oe5rnl/ESP32-ATT-C-LVGL8/docs/att_foto_bestueckt.jpg

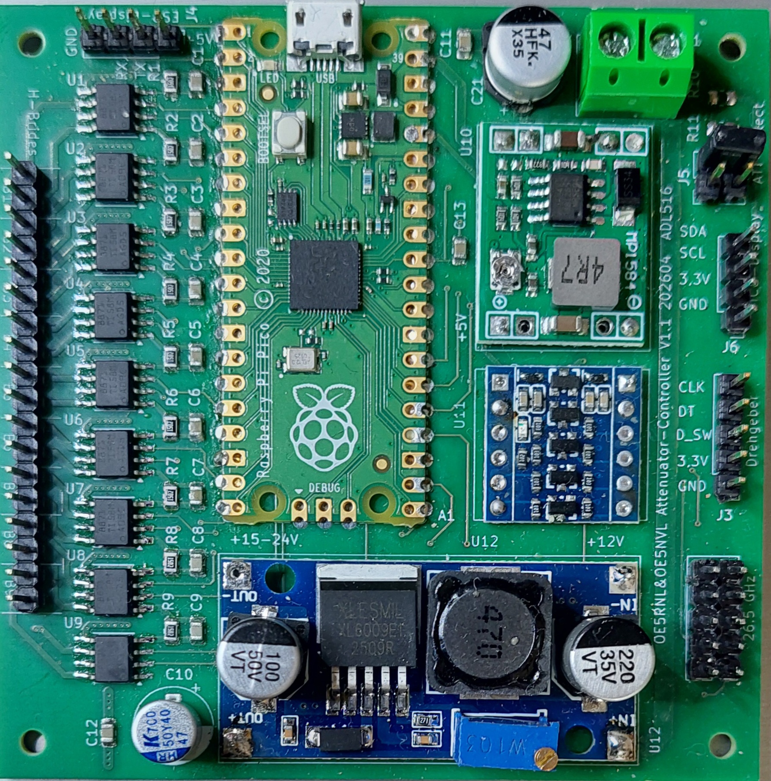
docs/att_foto_bestueckt.jpg
