oe5rnl/ESP32-ATT-C-LVGL8/pico/docu/Inkrementalgeber/71aFOMrbxAS._SL1500_.jpg

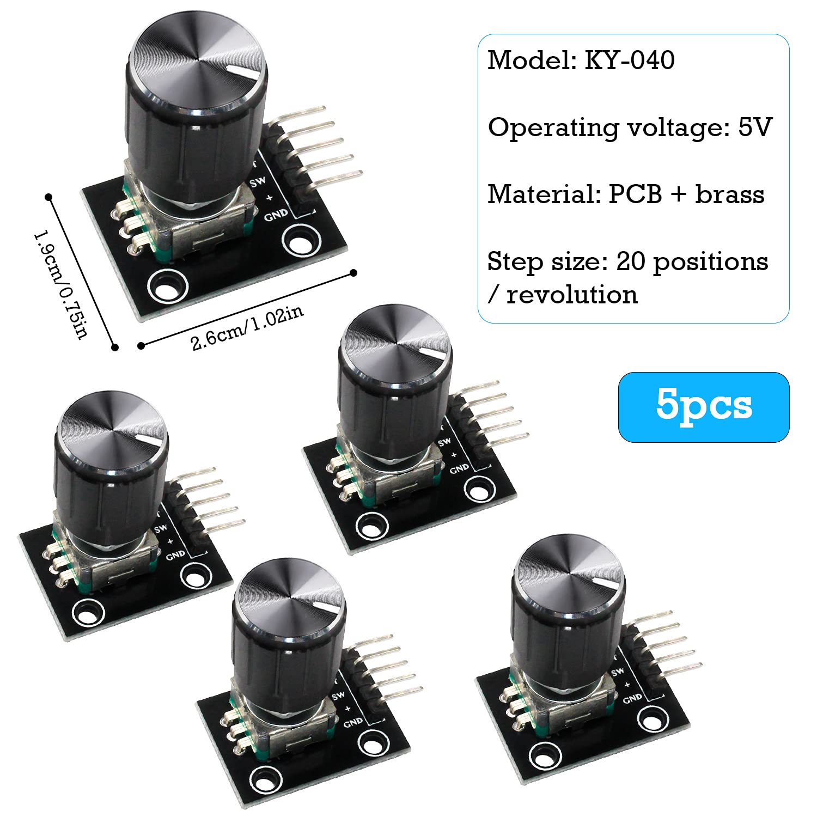
pico/docu/Inkrementalgeber/71aFOMrbxAS._SL1500_.jpg
