oe5rnl/ESP32-ATT-C-LVGL8/pico/docu/Inkrementalgeber/712gV1IUjDS._SL1500_.jpg

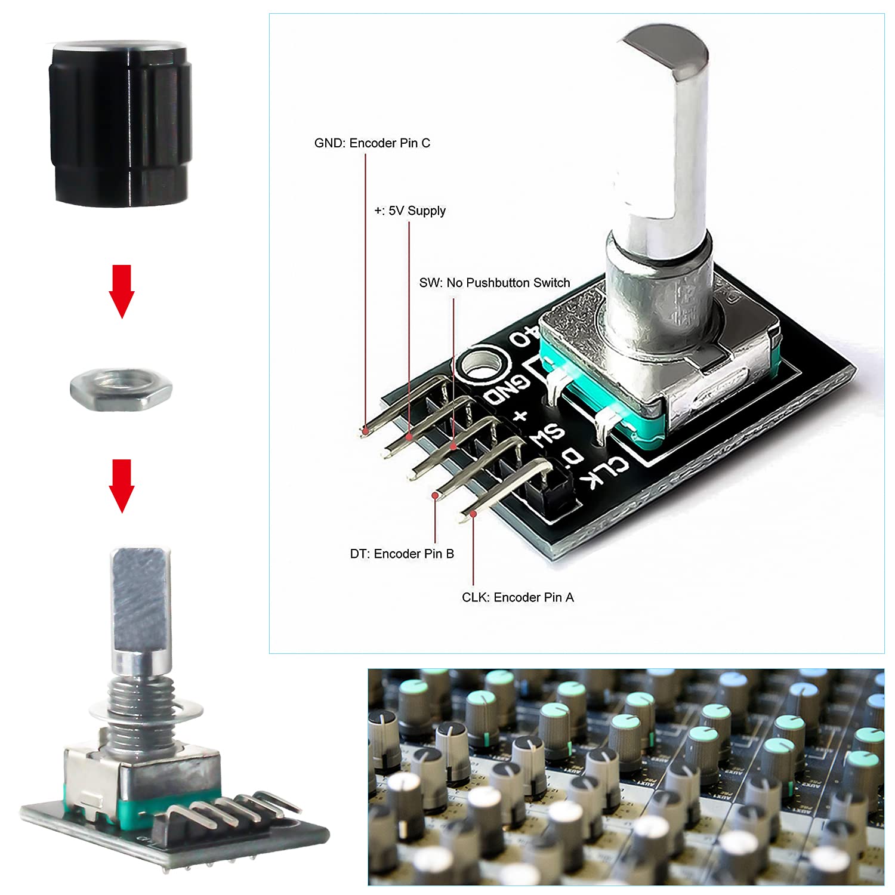
pico/docu/Inkrementalgeber/712gV1IUjDS._SL1500_.jpg
