oe5rnl/ESP32-ATT-C-LVGL8/pico/docu/raspberry-pi-pico-gpio.png

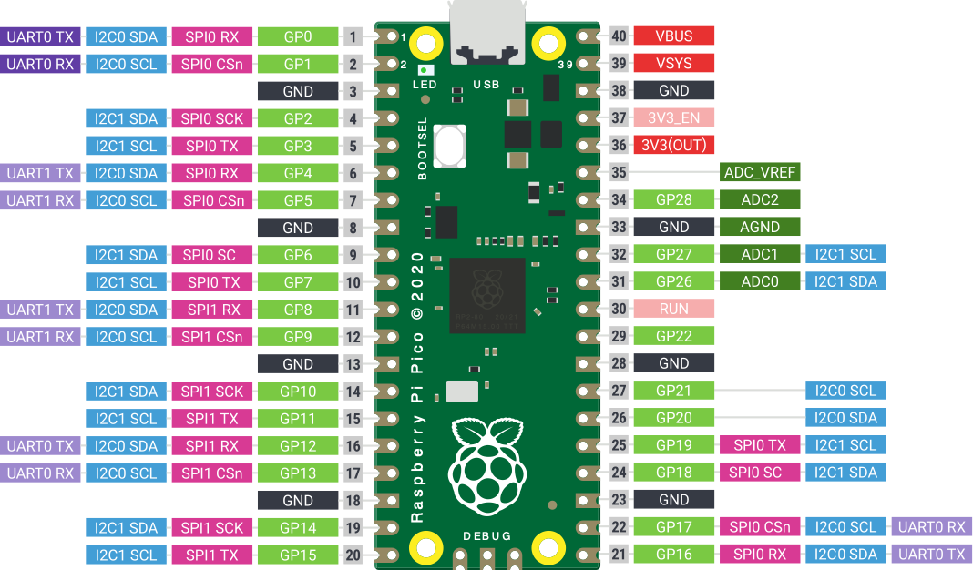
pico/docu/raspberry-pi-pico-gpio.png
