oe5rnl/ESP32-ATT-C-LVGL8/pico/src/big_digits.h

#ifndef BIG_DIGITS_H
#define BIG_DIGITS_H

#include <cstdint>

// Große Ziffern 24x32 Pixel
// Jede Ziffer ist 24 Pixel breit und 32 Pixel hoch
// Gespeichert als Array von 32 Bytes (jedes Byte = eine Zeile von 24 Pixeln, aufgeteilt in 3 Bytes)
const uint8_t big_digit_width = 24;
const uint8_t big_digit_height = 32;

// Für 24 Pixel Breite brauchen wir 3 Bytes pro Zeile
const uint8_t big_digits[10][32][3] = {
    // Ziffer 0
    {
        {0x00, 0xFF, 0x00}, {0x03, 0xFF, 0xC0}, {0x07, 0xFF, 0xE0}, {0x0F, 0xFF, 0xF0},
        {0x1F, 0x00, 0xF8}, {0x3E, 0x00, 0x7C}, {0x3C, 0x00, 0x3C}, {0x7C, 0x00, 0x3E},
        {0x78, 0x00, 0x1E}, {0x78, 0x00, 0x1E}, {0xF8, 0x00, 0x1F}, {0xF0, 0x00, 0x0F},
        {0xF0, 0x00, 0x0F}, {0xF0, 0x00, 0x0F}, {0xF0, 0x00, 0x0F}, {0xF0, 0x00, 0x0F},
        {0xF0, 0x00, 0x0F}, {0xF0, 0x00, 0x0F}, {0xF0, 0x00, 0x0F}, {0xF0, 0x00, 0x0F},
        {0xF8, 0x00, 0x1F}, {0x78, 0x00, 0x1E}, {0x78, 0x00, 0x1E}, {0x7C, 0x00, 0x3E},
        {0x3C, 0x00, 0x3C}, {0x3E, 0x00, 0x7C}, {0x1F, 0x00, 0xF8}, {0x0F, 0xFF, 0xF0},
        {0x07, 0xFF, 0xE0}, {0x03, 0xFF, 0xC0}, {0x00, 0xFF, 0x00}, {0x00, 0x00, 0x00}
    },
    // Ziffer 1
    {
        {0x00, 0x30, 0x00}, {0x00, 0x70, 0x00}, {0x00, 0xF0, 0x00}, {0x01, 0xF0, 0x00},
        {0x03, 0xF0, 0x00}, {0x07, 0xF0, 0x00}, {0x0F, 0xF0, 0x00}, {0x1F, 0xF0, 0x00},
        {0x3F, 0xF0, 0x00}, {0x7F, 0xF0, 0x00}, {0xFF, 0xF0, 0x00}, {0xFF, 0xF0, 0x00},
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
        {0x00, 0xFF, 0x1F}, {0x00, 0x00, 0x1E}, {0x00, 0x00, 0x1E}, {0x00, 0x00, 0x3E},
        {0x00, 0x00, 0x3C}, {0x3E, 0x00, 0x7C}, {0x1F, 0x00, 0xF8}, {0x0F, 0xFF, 0xF0},
        {0x07, 0xFF, 0xE0}, {0x03, 0xFF, 0xC0}, {0x00, 0xFF, 0x00}, {0x00, 0x00, 0x00}
    }
};

#endif // BIG_DIGITS_H
