oe5rnl/ESP32-ATT-C-LVGL8/pico/src/att_135db.cpp

#include "att_135db.h"
#include "SSD1306.h"
#include <Arduino.h>

extern SSD1306 display;

/* Mapping pad value → physical relay slot, ermittelt durch Messung:
 *   U1 (GPIO2/3)   = 5 dB
 *   U2 (GPIO6/7)   = 20 dB   (Header-Name irrefuehrend "10dB")
 *   U3 (GPIO8/9)   = 40 dB   (Header-Name irrefuehrend "20B")
 *   U4 (GPIO10/11) = 20 dB
 *   U5 (GPIO12/13) = 10 dB   (Header-Name irrefuehrend "40A")
 *   U6 (GPIO14/15) = 40 dB
 */
const Att135dB::RelayDef Att135dB::_relays[] = {
    {"40A",  GPIO_135DB_40DB_ON_A,  GPIO_135DB_40DB_OFF_A }, /* U3 = 40 dB */
    {"20A",  GPIO_135DB_20DB_ON_A,  GPIO_135DB_20DB_OFF_A }, /* U4 = 20 dB */
    {"5dB",  GPIO_135DB_5DB_ON,     GPIO_135DB_5DB_OFF    }, /* U1 =  5 dB  */
    {"20B",  GPIO_135DB_20DB_ON_B,  GPIO_135DB_20DB_OFF_B }, /* U2 = 20 dB */
    {"10dB", GPIO_135DB_10DB_ON,    GPIO_135DB_10DB_OFF   }, /* U5 = 10 dB */
    {"40B",  GPIO_135DB_40DB_ON_B,  GPIO_135DB_40DB_OFF_B }, /* U6 = 40 dB */
    {"RF",   GPIO_135DB_RF_ON,      GPIO_135DB_RF_OFF     }, /* U7 = RF    */
};

/* ---- private helpers ---- */

void Att135dB::pulse_pin(int pin)
{
    digitalWrite(pin, HIGH);
    delay(20);
    digitalWrite(pin, LOW);
}

void Att135dB::pulse(int idx, bool activate)
{
    pulse_pin(activate ? _relays[idx].on_pin : _relays[idx].off_pin);
}

/* ---- public interface ---- */

void Att135dB::setup()
{
    for(int i = 0; i < RELAY_COUNT; i++) {
        pinMode(_relays[i].on_pin,  OUTPUT);
        pinMode(_relays[i].off_pin, OUTPUT);
        digitalWrite(_relays[i].on_pin,  LOW);
        digitalWrite(_relays[i].off_pin, LOW);
    }
    /* Bring all bistable relays to OFF state in parallel */
    for(int i = 0; i < RELAY_COUNT; i++) {
        digitalWrite(_relays[i].off_pin, HIGH);
        _states[i] = false;
    }
    delay(20);
    for(int i = 0; i < RELAY_COUNT; i++) {
        digitalWrite(_relays[i].off_pin, LOW);
    }
    /* Relay 7 (RF) always ON – GPIO inverted: pulse OFF pin to activate */
    digitalWrite(_relays[6].off_pin, HIGH);
    delay(20);
    digitalWrite(_relays[6].off_pin, LOW);
    _states[6] = true;

}

void Att135dB::apply(int32_t dv)
{
    int32_t att = (dv / step_db()) * step_db();
    if(att > max_db()) att = max_db();
    if(att < 0) att = 0;

    /* Greedy decomposition: 40A → 40B → 20A → 20B → 10 → 5 */
    int32_t rem = att;
    bool a40a = (rem >= 40); if(a40a) rem -= 40;
    bool a40b = (rem >= 40); if(a40b) rem -= 40;
    bool a20a = (rem >= 20); if(a20a) rem -= 20;
    bool a20b = (rem >= 20); if(a20b) rem -= 20;
    bool a10  = (rem >= 10); if(a10)  rem -= 10;
    bool a5   = (rem >= 5);

    /* relay order must match _relays[]: 40A,20A,5dB,20B,10dB,40B,RF
     * RF (index 6) is NOT touched here – it is controlled separately via set_rf() */
    bool desired[RELAY_COUNT] = {a40a, a20a, a5, a20b, a10, a40b, _states[6]};

    /* Set all needed pins HIGH in parallel */
    bool any_change = false;
    for(int i = 0; i < RELAY_COUNT; i++) {
        if(desired[i] != _states[i]) {
            int pin = desired[i] ? _relays[i].on_pin : _relays[i].off_pin;
            digitalWrite(pin, HIGH);
            any_change = true;
        }
    }
    if(any_change) {
        delay(20);
        for(int i = 0; i < RELAY_COUNT; i++) {
            if(desired[i] != _states[i]) {
                int pin = desired[i] ? _relays[i].on_pin : _relays[i].off_pin;
                digitalWrite(pin, LOW);
                _states[i] = desired[i];
            }
        }
    }

    // Serial.print("ATT 135dB: ");
    // Serial.print(att);
    // Serial.print(" dB  [40A="); Serial.print(a40a);
    // Serial.print(" 20A=");      Serial.print(a20a);
    // Serial.print(" 5=");        Serial.print(a5);
    // Serial.print(" 20B=");      Serial.print(a20b);
    // Serial.print(" 10=");       Serial.print(a10);
    // Serial.print(" 40B=");      Serial.print(a40b);
    // Serial.print(" RF=");       Serial.print(rf);
    // Serial.println("]");
}

void Att135dB::set_rf(bool on)
{
    if(_states[6] == on) return;
    pulse(6, !on);   /* GPIO inverted: ON-state uses OFF-pin and vice versa */
    _states[6] = on;
}

/* ---- Safety watchdog ---- */

void Att135dB::poll()
{
    unsigned long now = millis();

    for(int i = 0; i < RELAY_COUNT; i++) {
        const int pins[2] = { _relays[i].off_pin, _relays[i].on_pin };
        for(int p = 0; p < 2; p++) {
            if(digitalRead(pins[p]) == HIGH) {
                if(_pin_armed_ms[i][p] == 0) {
                    /* First sample: record the moment this pin went (or was found) HIGH */
                    _pin_armed_ms[i][p] = now ? now : 1UL;
                } else if((now - _pin_armed_ms[i][p]) >= PIN_MAX_HIGH_MS) {
                    /* Limit exceeded – pull LOW immediately */
                    digitalWrite(pins[p], LOW);
                    _pin_armed_ms[i][p] = 0;
                    Serial.print("[WATCHDOG] att_135db: GPIO");
                    Serial.print(pins[p]);
                    Serial.print(" (relay ");
                    Serial.print(_relays[i].name);
                    Serial.println(p == 1 ? " ON) forced LOW" : " OFF) forced LOW");
                }
            } else {
                _pin_armed_ms[i][p] = 0;
            }
        }
    }
}
